francisengelmann/FabScan/sources/FabScanMac/FabScan3D/calib1.jpg

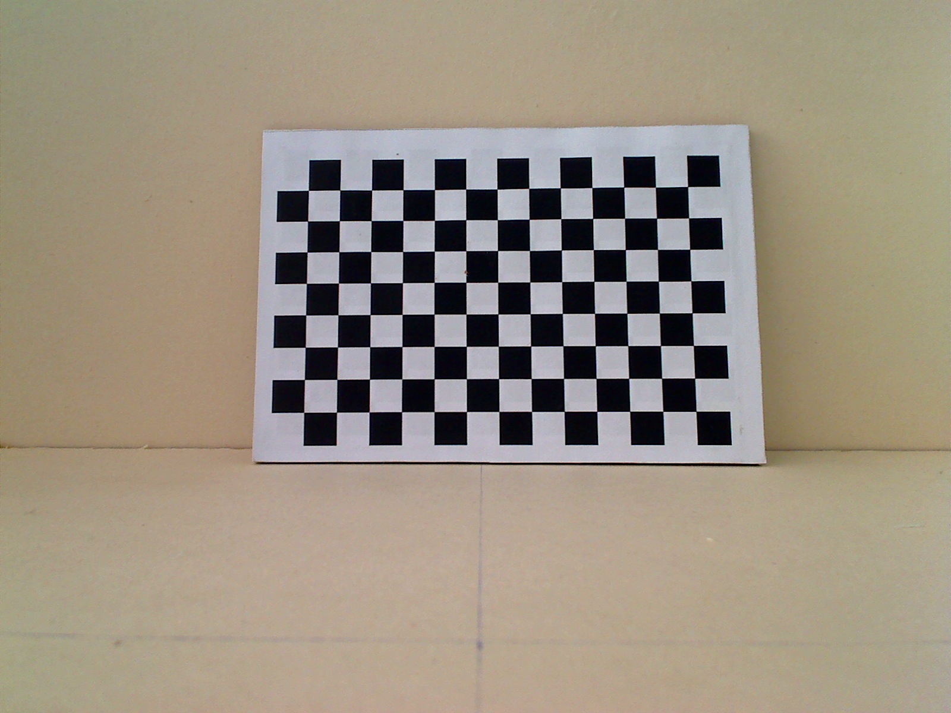
sources/FabScanMac/FabScan3D/calib1.jpg
