francisengelmann/FabScan/sources/FabScanMac/FabScan3D/calib2.jpg

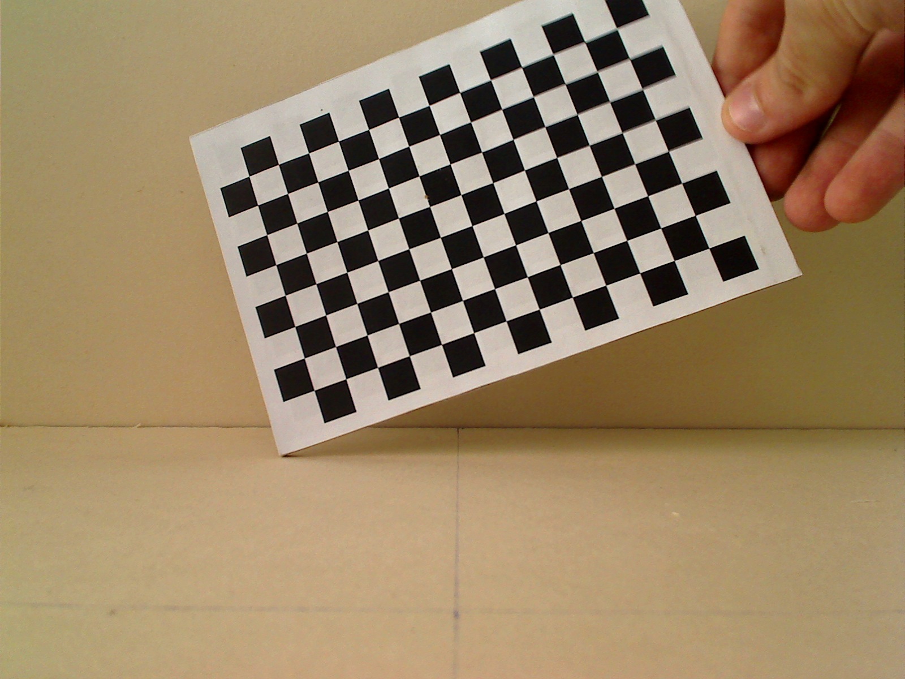
sources/FabScanMac/FabScan3D/calib2.jpg
