francisengelmann/FabScan/sources/FabScanMac/FabScan3D/calib3.jpg

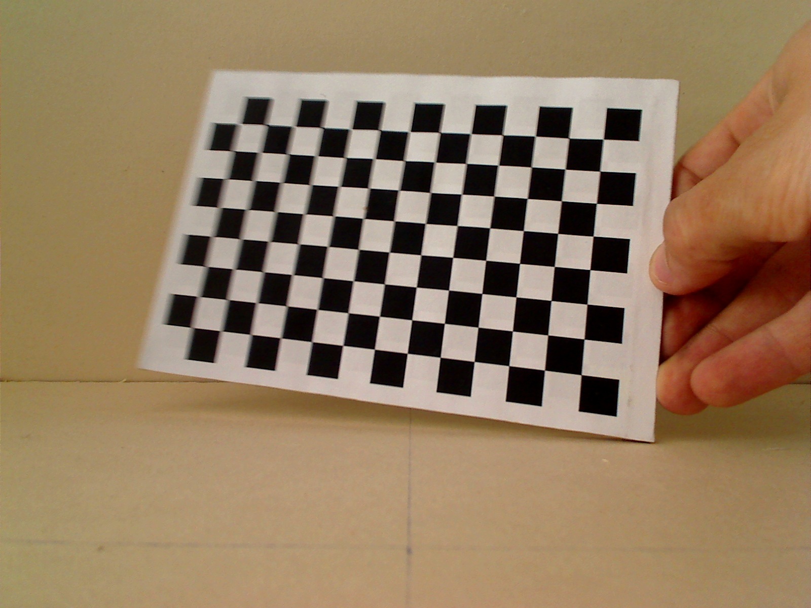
sources/FabScanMac/FabScan3D/calib3.jpg
