francisengelmann/FabScan/sources/FabScanMac/FabScan3D/calib4.jpg

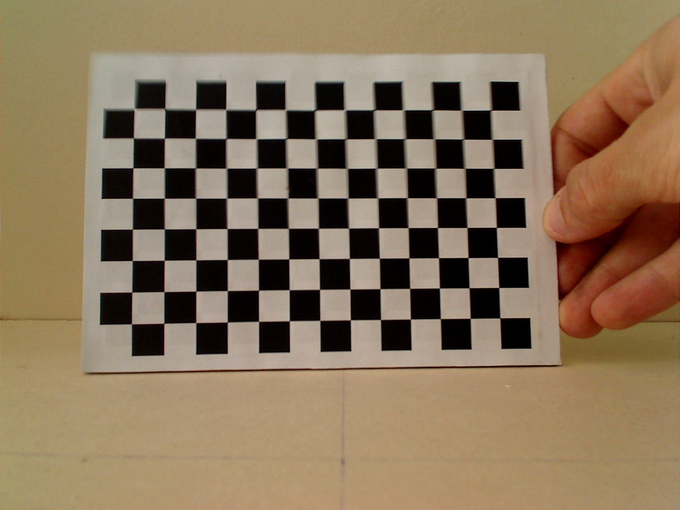
sources/FabScanMac/FabScan3D/calib4.jpg
