francisengelmann/FabScan/sources/FabScanMac/FabScan3D/calib5.jpg

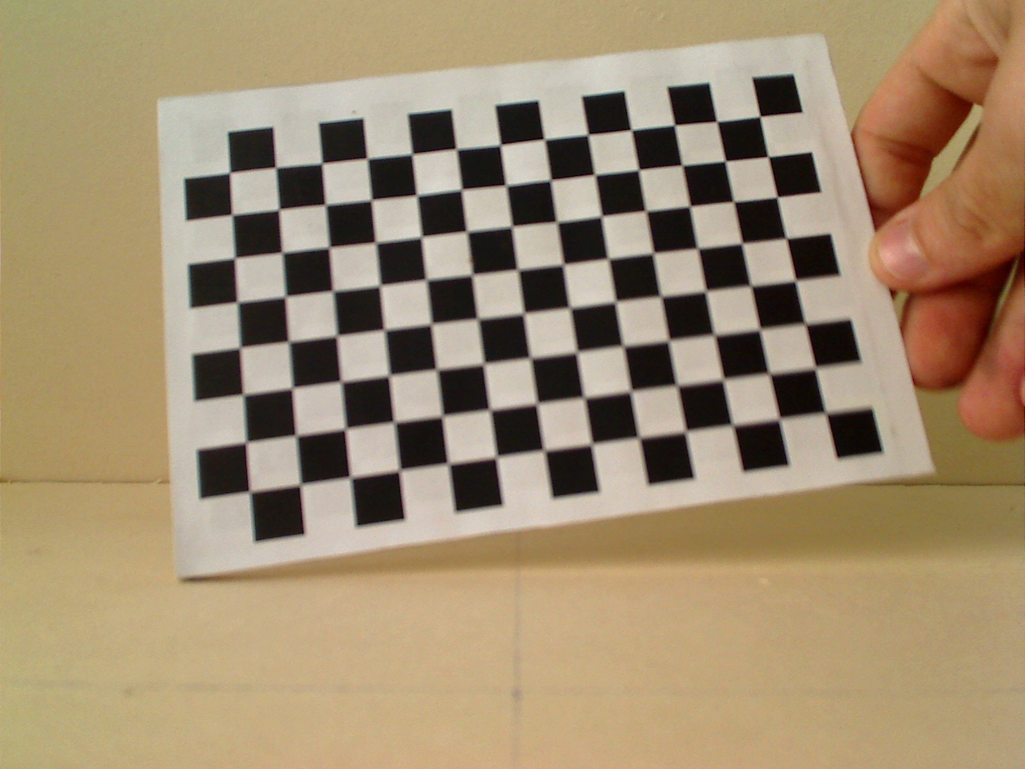
sources/FabScanMac/FabScan3D/calib5.jpg
