francisengelmann/FabScan/sources/FabScanMac/FabScan3D/calib6.jpg

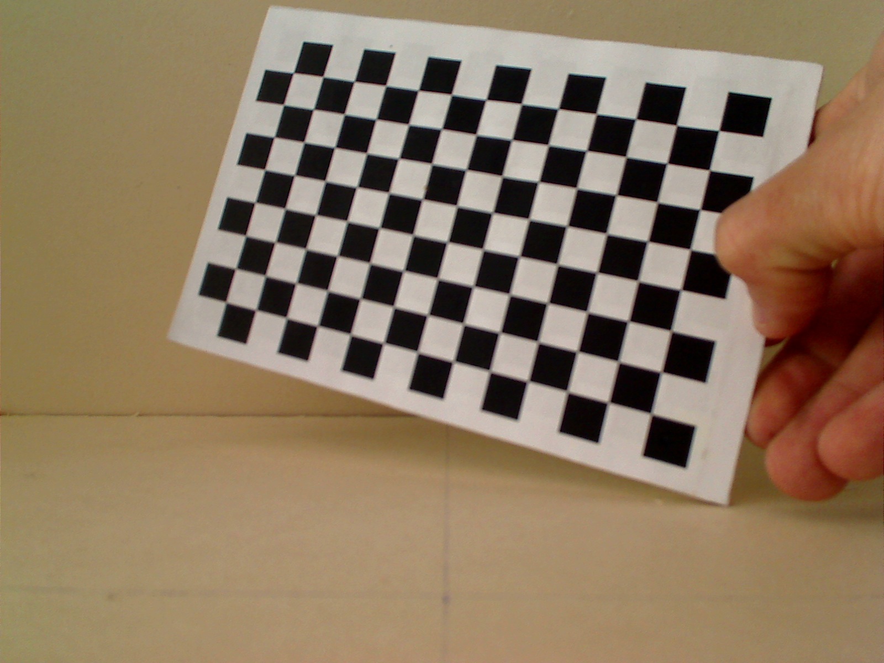
sources/FabScanMac/FabScan3D/calib6.jpg
