francisengelmann/FabScan/sources/FabScanMac/FabScan3D/calib7.jpg

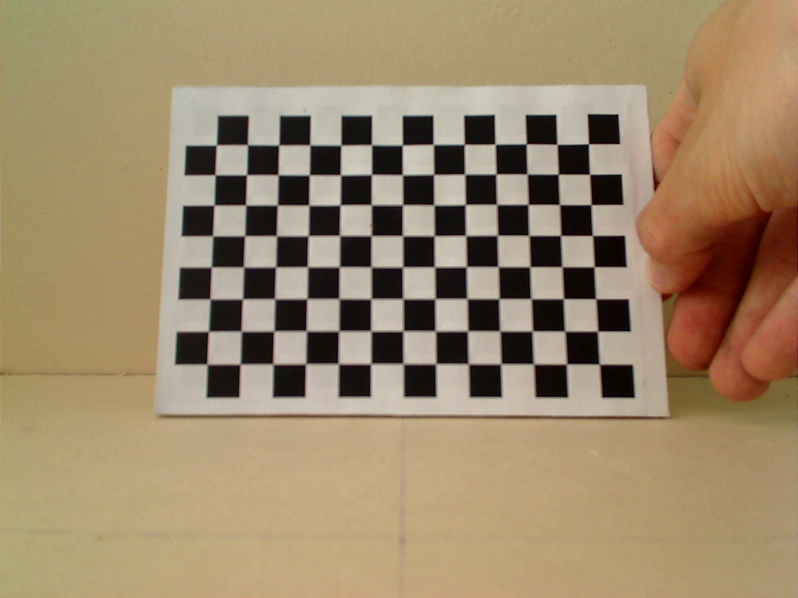
sources/FabScanMac/FabScan3D/calib7.jpg
