francisengelmann/FabScan/sources/FabScanMac/FabScan3D/calib8.jpg

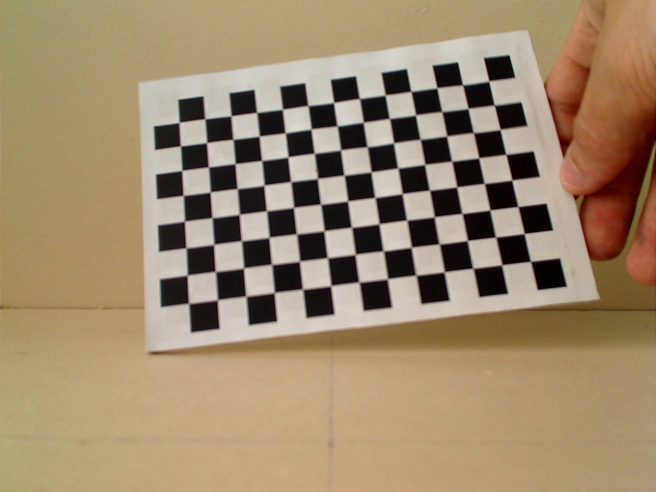
sources/FabScanMac/FabScan3D/calib8.jpg
