francisengelmann/FabScan/sources/FabScanMac/FabScan3D/calib9.jpg

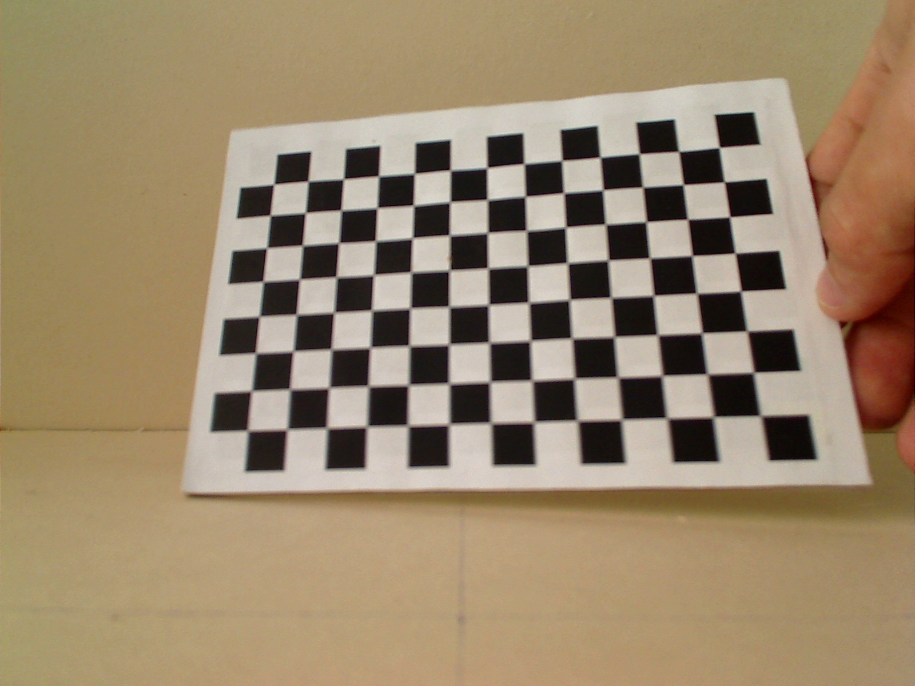
sources/FabScanMac/FabScan3D/calib9.jpg
