francisengelmann/FabScan/sources/FabScanMac/FabScan3D/calib10.jpg

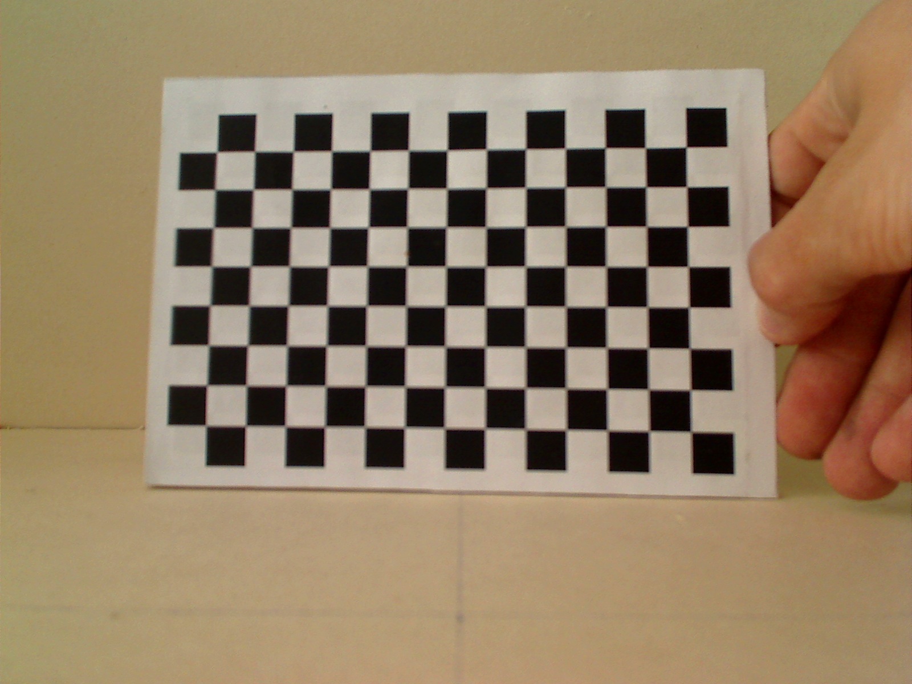
sources/FabScanMac/FabScan3D/calib10.jpg
