francisengelmann/FabScan/sources/FabScanMac/FabScan3D/calib.jpg

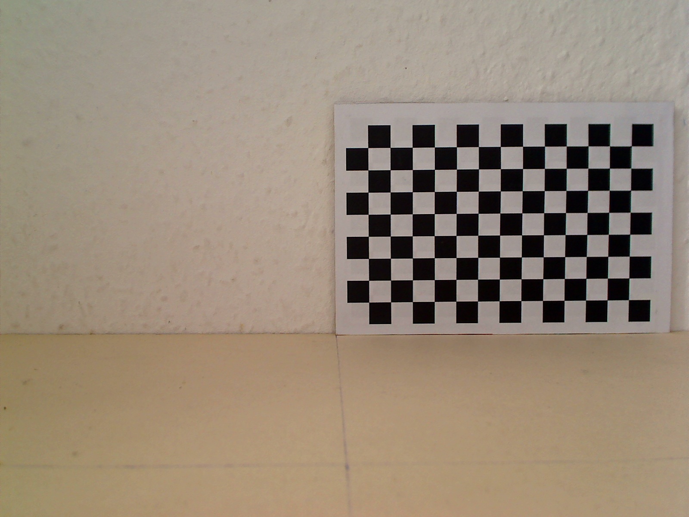
sources/FabScanMac/FabScan3D/calib.jpg
